HansAchterbahn/pt100-thermometer/Simulation/LTSpice/Thermometer-PT100-LTSpice.asc

C1: cap; 100n
C2: cap; 100n
PT100: res; 100R
R1: res; 1.65k
R2: res; 1.65k
R3: res; 3k
R4: res; 24.7k
R5: res; 5.49k
R6: res; 24.7k
R7: res; 24.7k
R8: res; 24.7k
R9: res; 24.7k
R10: res; 24.7k
R11: res; 15k
R13: res; 15k
R14: res; 15k
R15: res; 1.8k
R16: res; 1.8k
R18: res; 4.7k
R19: res; 9.1k
U1: UniversalOpamp2
U2: UniversalOpamp2
U3: UniversalOpamp2
U4: UniversalOpamp2
U5: UniversalOpamp2
U6: UniversalOpamp2
U8: UniversalOpamp2
V1: voltage; 5
Named nets: Ub+, Ub-, U_Ref, Sym_GND, ADU_IN, U_Instrument, 0
.tran 10us
Konstantstromquelle
Instrumentenverstärker
Offset-Korrektur
Symmetrische Spannungsversorgung
Referenzspannung zur Offsetkorrektur des PT100
2.5k 
|---------------|
In-
In+
Out
Ref.
Beachte:
------------
Der PT100 kann Werte zwischen 80 und 140 Ohm annehmen.
Das entspricht einer Temperaturspanne von -50 bis 100°C.
 
Mehr Informationen:
-----------------------------
https://aetzenloetenprogrammieren.blogspot.de/2017/01/ein-
einfaches-thermometer-mit-pt100.html
 
https://github.com/HansAchterbahn/pt100-thermometer
Rg1
Rg2
